hansiglaser/prjblinkenlights/workspace/PrjBlinkenlights/utils.h

/*
 * utils.h
 *
 *  Created on: Dec 9, 2012
 *      Author: hansi
 */

#ifndef UTILS_H_
#define UTILS_H_

#include <stdint.h>

uint16_t Int2BCD(uint16_t i);

void delay_ms(int ms);

#endif /* UTILS_H_ */
